eric-wieser/catan-table/units.scad

mm = 1;
in = 25.4;
ft = 12 * in;
